Ventuj/RC-Car/Docs/Img/Bottom-Side.png

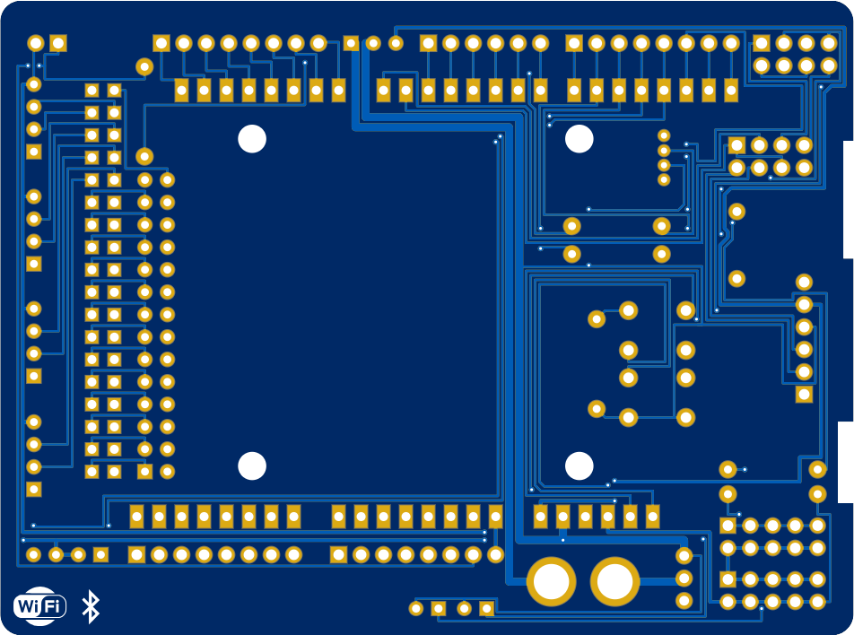
Docs/Img/Bottom-Side.png
