Ventuj/RC-Car/Docs/Img/PCB-Bottom Side.png

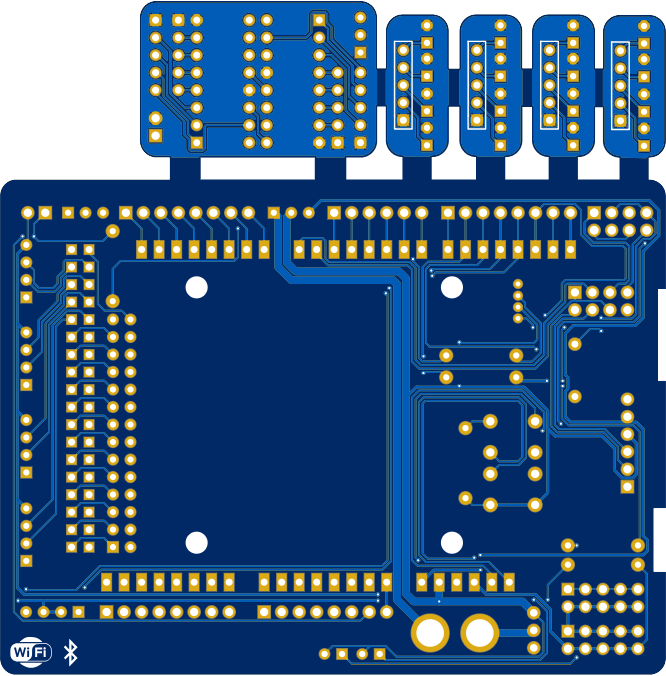
Docs/Img/PCB-Bottom Side.png
