Ventuj/RC-Car/Docs/Img/PCB-Top Side.png

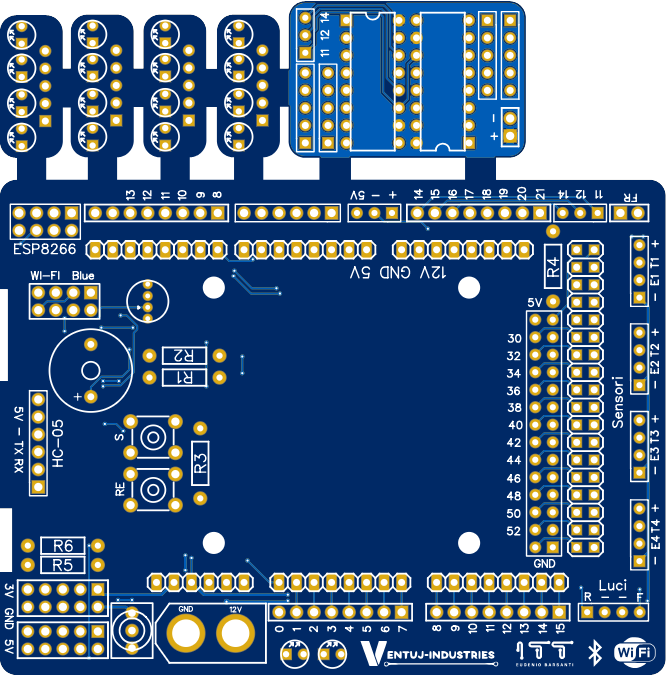
Docs/Img/PCB-Top Side.png
