Ventuj/RC-Car/Docs/Img/PCB-Top.png

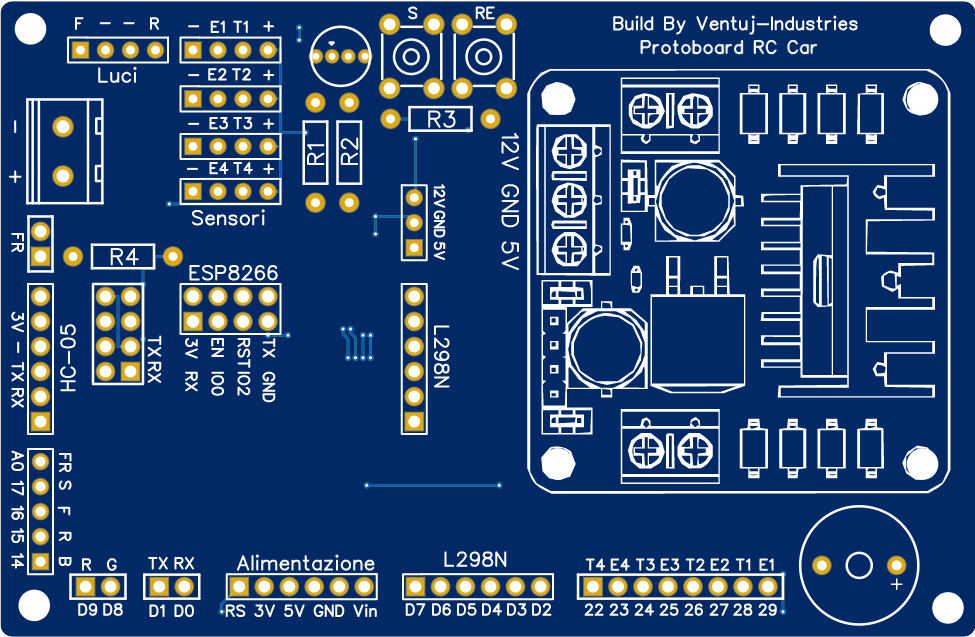
Docs/Img/PCB-Top.png
