Ventuj/RC-Car/Docs/Img/photo_2020-02-13_14-54-27.jpg

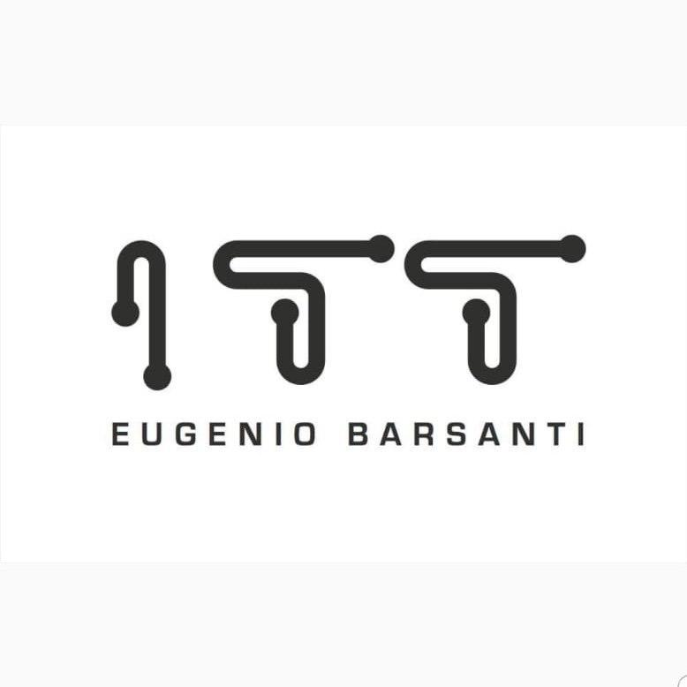
Docs/Img/photo_2020-02-13_14-54-27.jpg
