Ventuj/RC-Car/Docs/Img/Top-Side.png

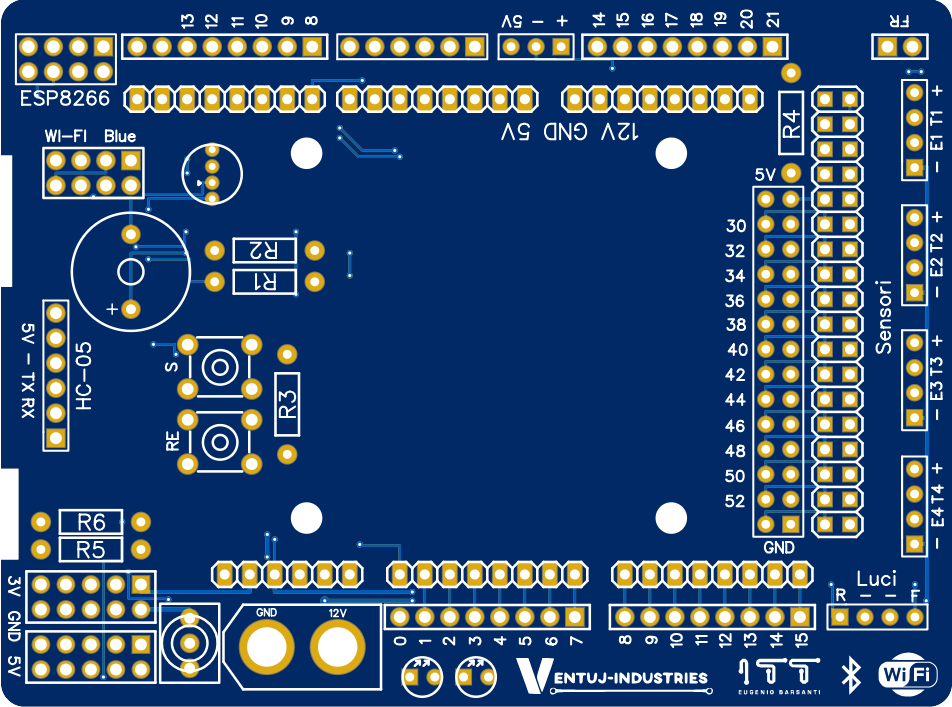
Docs/Img/Top-Side.png
